milovanpms/talk-e/software/i2c_oled/main/i2c_oled_example_main.c

/*
 * SPDX-FileCopyrightText: 2021-2025 Espressif Systems (Shanghai) CO LTD
 *
 * SPDX-License-Identifier: CC0-1.0
 */

#include <stdio.h>
#include <unistd.h>
#include <string.h>
#include <sys/lock.h>
#include <sys/param.h>
#include "freertos/FreeRTOS.h"
#include "freertos/task.h"
#include "esp_timer.h"
#include "esp_lcd_panel_io.h"
#include "esp_lcd_panel_ops.h"
#include "esp_err.h"
#include "esp_check.h"
#include "esp_log.h"
#include "driver/i2c_master.h"
#include "lvgl.h"
#include "esp_lcd_panel_vendor.h"

static const char *TAG = "example";

#define I2C_BUS_PORT  0

////////////////////////////////////////////////////////////////////////////////////////////////////////////////////////
//////////////////// Please update the following configuration according to your LCD spec //////////////////////////////
////////////////////////////////////////////////////////////////////////////////////////////////////////////////////////
#define EXAMPLE_LCD_PIXEL_CLOCK_HZ    (400 * 1000)
#define EXAMPLE_PIN_NUM_SDA           21
#define EXAMPLE_PIN_NUM_SCL           22
#define EXAMPLE_PIN_NUM_RST           -1
#define EXAMPLE_I2C_HW_ADDR           0x3C

// The pixel number in horizontal and vertical
#define EXAMPLE_LCD_H_RES              128
#define EXAMPLE_LCD_V_RES              64
// Bit number used to represent command and parameter
#define EXAMPLE_LCD_CMD_BITS           8
#define EXAMPLE_LCD_PARAM_BITS         8

#define EXAMPLE_LVGL_TICK_PERIOD_MS    5
#define EXAMPLE_LVGL_TASK_STACK_SIZE   (4 * 1024)
#define EXAMPLE_LVGL_TASK_PRIORITY     2
#define EXAMPLE_LVGL_PALETTE_SIZE      8
#define EXAMPLE_LVGL_TASK_MAX_DELAY_MS 500
#define EXAMPLE_LVGL_TASK_MIN_DELAY_MS 1000 / CONFIG_FREERTOS_HZ

// To use LV_COLOR_FORMAT_I1, we need an extra buffer to hold the converted data
static uint8_t oled_buffer[EXAMPLE_LCD_H_RES * EXAMPLE_LCD_V_RES / 8];
// LVGL library is not thread-safe, this example will call LVGL APIs from different tasks, so use a mutex to protect it
static _lock_t lvgl_api_lock;

extern void example_lvgl_demo_ui(lv_disp_t *disp);

typedef struct {
    esp_lcd_panel_handle_t panel;
    esp_lcd_panel_io_handle_t io;
} example_oled_ctx_t;

static example_oled_ctx_t s_oled_ctx;

static esp_err_t example_draw_full_frame_sh1106(esp_lcd_panel_io_handle_t io, const uint8_t *frame, uint16_t hor_res, uint16_t ver_res)
{
    uint8_t pages = ver_res / 8;
    for (uint8_t page = 0; page < pages; page++) {
        // SH1106 has 132 columns RAM, visible 128 columns are shifted by +2.
        ESP_RETURN_ON_ERROR(esp_lcd_panel_io_tx_param(io, 0xB0 | page, NULL, 0), TAG, "set page failed");
        ESP_RETURN_ON_ERROR(esp_lcd_panel_io_tx_param(io, 0x02, NULL, 0), TAG, "set lower column failed");
        ESP_RETURN_ON_ERROR(esp_lcd_panel_io_tx_param(io, 0x10, NULL, 0), TAG, "set higher column failed");
        ESP_RETURN_ON_ERROR(esp_lcd_panel_io_tx_color(io, -1, frame + page * hor_res, hor_res), TAG, "tx page failed");
    }
    return ESP_OK;
}

static void example_lvgl_flush_cb(lv_display_t *disp, const lv_area_t *area, uint8_t *px_map)
{
    example_oled_ctx_t *oled_ctx = lv_display_get_user_data(disp);

    // This is necessary because LVGL reserves 2 x 4 bytes in the buffer, as these are assumed to be used as a palette. Skip the palette here
    // More information about the monochrome, please refer to https://docs.lvgl.io/9.2/porting/display.html#monochrome-displays
    px_map += EXAMPLE_LVGL_PALETTE_SIZE;

    uint16_t hor_res = lv_display_get_physical_horizontal_resolution(disp);
    uint16_t ver_res = lv_display_get_physical_vertical_resolution(disp);
    int x1 = area->x1;
    int x2 = area->x2;
    int y1 = area->y1;
    int y2 = area->y2;
    uint32_t src_stride = lv_draw_buf_width_to_stride(lv_area_get_width(area), LV_COLOR_FORMAT_I1);

    for (int y = y1; y <= y2; y++) {
        for (int x = x1; x <= x2; x++) {
            /* The order of bits is MSB first
                        MSB           LSB
               bits      7 6 5 4 3 2 1 0
               pixels    0 1 2 3 4 5 6 7
                        Left         Right
            */
            int src_x = x - x1;
            int src_y = y - y1;
            bool chroma_color = ((px_map[src_stride * src_y + (src_x >> 3)] & (1 << (7 - (src_x % 8)))) != 0);

            /* Write to the buffer as required for the display.
            * It writes only 1-bit for monochrome displays mapped vertically.*/
            uint8_t *buf = oled_buffer + (y >> 3) * hor_res + (x);
            if (chroma_color) {
                (*buf) &= ~(1 << (y % 8));
            } else {
                (*buf) |= (1 << (y % 8));
            }
        }
    }
    // Send full frame from the persistent monochrome buffer to avoid partial-area packing mismatch.
    esp_err_t ret = example_draw_full_frame_sh1106(oled_ctx->io, oled_buffer, hor_res, ver_res);
    if (ret != ESP_OK) {
        ESP_LOGE(TAG, "SH1106 full-frame flush failed: %s", esp_err_to_name(ret));
    }
    lv_display_flush_ready(disp);
}

static void example_increase_lvgl_tick(void *arg)
{
    /* Tell LVGL how many milliseconds has elapsed */
    lv_tick_inc(EXAMPLE_LVGL_TICK_PERIOD_MS);
}

static void example_lvgl_port_task(void *arg)
{
    ESP_LOGI(TAG, "Starting LVGL task");
    uint32_t time_till_next_ms = 0;
    while (1) {
        _lock_acquire(&lvgl_api_lock);
        time_till_next_ms = lv_timer_handler();
        _lock_release(&lvgl_api_lock);
        // in case of triggering a task watch dog time out
        time_till_next_ms = MAX(time_till_next_ms, EXAMPLE_LVGL_TASK_MIN_DELAY_MS);
        // in case of lvgl display not ready yet
        time_till_next_ms = MIN(time_till_next_ms, EXAMPLE_LVGL_TASK_MAX_DELAY_MS);
        usleep(1000 * time_till_next_ms);
    }
}

void app_main(void)
{
    ESP_LOGI(TAG, "Initialize I2C bus");
    i2c_master_bus_handle_t i2c_bus = NULL;
    i2c_master_bus_config_t bus_config = {
        .clk_source = I2C_CLK_SRC_DEFAULT,
        .glitch_ignore_cnt = 7,
        .i2c_port = I2C_BUS_PORT,
        .sda_io_num = EXAMPLE_PIN_NUM_SDA,
        .scl_io_num = EXAMPLE_PIN_NUM_SCL,
        .flags.enable_internal_pullup = true,
    };
    ESP_ERROR_CHECK(i2c_new_master_bus(&bus_config, &i2c_bus));

    ESP_LOGI(TAG, "Install panel IO");
    esp_lcd_panel_io_handle_t io_handle = NULL;
    esp_lcd_panel_io_i2c_config_t io_config = {
        .dev_addr = EXAMPLE_I2C_HW_ADDR,
        .scl_speed_hz = EXAMPLE_LCD_PIXEL_CLOCK_HZ,
        .control_phase_bytes = 1,               // According to SSD1306 datasheet
        .lcd_cmd_bits = EXAMPLE_LCD_CMD_BITS,   // According to SSD1306 datasheet
        .lcd_param_bits = EXAMPLE_LCD_PARAM_BITS, // According to SSD1306 datasheet
        .dc_bit_offset = 6,                     // According to SSD1306 datasheet
    };
    ESP_ERROR_CHECK(esp_lcd_new_panel_io_i2c(i2c_bus, &io_config, &io_handle));

    ESP_LOGI(TAG, "Install SSD1306 panel driver");
    esp_lcd_panel_handle_t panel_handle = NULL;
    esp_lcd_panel_dev_config_t panel_config = {
        .bits_per_pixel = 1,
        .reset_gpio_num = EXAMPLE_PIN_NUM_RST,
    };
    esp_lcd_panel_ssd1306_config_t ssd1306_config = {
        .height = EXAMPLE_LCD_V_RES,
    };
    panel_config.vendor_config = &ssd1306_config;
    ESP_ERROR_CHECK(esp_lcd_new_panel_ssd1306(io_handle, &panel_config, &panel_handle));

    ESP_ERROR_CHECK(esp_lcd_panel_reset(panel_handle));
    ESP_ERROR_CHECK(esp_lcd_panel_init(panel_handle));
    ESP_ERROR_CHECK(esp_lcd_panel_mirror(panel_handle, true, true)); // Pivoter l'écran de 180 deg
    ESP_ERROR_CHECK(esp_lcd_panel_disp_on_off(panel_handle, true));
    memset(oled_buffer, 0x00, sizeof(oled_buffer));
    ESP_ERROR_CHECK(example_draw_full_frame_sh1106(io_handle, oled_buffer, EXAMPLE_LCD_H_RES, EXAMPLE_LCD_V_RES));

    ESP_LOGI(TAG, "Initialize LVGL");
    lv_init();
    // create a lvgl display
    lv_display_t *display = lv_display_create(EXAMPLE_LCD_H_RES, EXAMPLE_LCD_V_RES);
    s_oled_ctx.panel = panel_handle;
    s_oled_ctx.io = io_handle;
    // associate OLED context to the display
    lv_display_set_user_data(display, &s_oled_ctx);
    // create draw buffer
    void *buf = NULL;
    ESP_LOGI(TAG, "Allocate separate LVGL draw buffers");
    // LVGL reserves 2 x 4 bytes in the buffer, as these are assumed to be used as a palette.
    size_t draw_buffer_sz = EXAMPLE_LCD_H_RES * EXAMPLE_LCD_V_RES / 8 + EXAMPLE_LVGL_PALETTE_SIZE;
    buf = heap_caps_calloc(1, draw_buffer_sz, MALLOC_CAP_INTERNAL | MALLOC_CAP_8BIT);
    assert(buf);

    // LVGL9 suooprt new monochromatic format.
    lv_display_set_color_format(display, LV_COLOR_FORMAT_I1);
    // initialize LVGL draw buffers
    lv_display_set_buffers(display, buf, NULL, draw_buffer_sz, LV_DISPLAY_RENDER_MODE_FULL);
    // set the callback which can copy the rendered image to an area of the display
    lv_display_set_flush_cb(display, example_lvgl_flush_cb);

    ESP_LOGI(TAG, "Use esp_timer as LVGL tick timer");
    const esp_timer_create_args_t lvgl_tick_timer_args = {
        .callback = &example_increase_lvgl_tick,
        .name = "lvgl_tick"
    };
    esp_timer_handle_t lvgl_tick_timer = NULL;
    ESP_ERROR_CHECK(esp_timer_create(&lvgl_tick_timer_args, &lvgl_tick_timer));
    ESP_ERROR_CHECK(esp_timer_start_periodic(lvgl_tick_timer, EXAMPLE_LVGL_TICK_PERIOD_MS * 1000));

    ESP_LOGI(TAG, "Create LVGL task");
    xTaskCreate(example_lvgl_port_task, "LVGL", EXAMPLE_LVGL_TASK_STACK_SIZE, NULL, EXAMPLE_LVGL_TASK_PRIORITY, NULL);

    ESP_LOGI(TAG, "Display LVGL Scroll Text");
    // Lock the mutex due to the LVGL APIs are not thread-safe
    _lock_acquire(&lvgl_api_lock);
    example_lvgl_demo_ui(display);
    _lock_release(&lvgl_api_lock);
}
